mroetsc/krypton-kbd/ergogen/cad/kali_hotswap.step

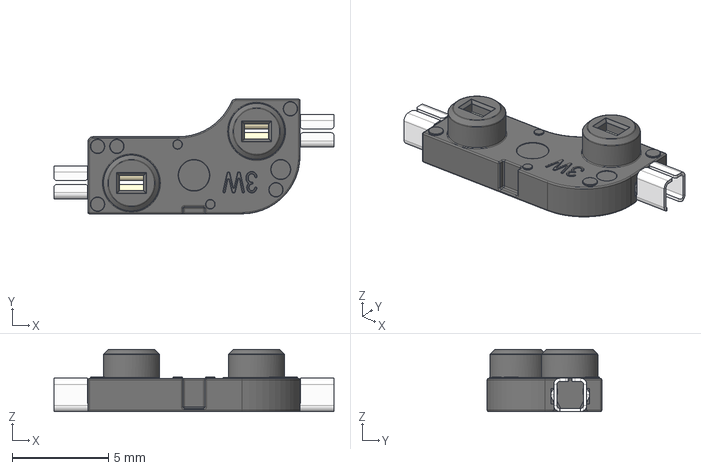
[picture p16: CAD file, 2025-02-28]
ergogen/cad/kali_hotswap.step
14.5 x 5.95 x 3.22 mm
